ThomHPL/Open80017a/Simulations/lm13700_test.asc

I1: current; 1m
R3: res; 1Meg
R4: res; 1k
R5: res; 1k
U1: LM13700
V1: voltage; 15
V2: voltage; SINE(0 100m 1k); AC 1m
V3: voltage; -15
Named nets: 0, VCC, VSS
.lib lm13700.sub
;tran 1u 10m
.dc I1 0.05m 1m .01m
