ThomHPL/Open80017a/Simulations/open_80017A.asc

C1: cap; 100n
C2: cap; 47p
C3: cap; 100n
C4: cap; 270p
C5: cap; 270p
C6: cap; 270p
C7: cap; 270p
C8: cap; 47p
C9: cap; 1µ
C10: cap; 270p
I1: current; 37µ
Q1: pnp; 2N2907
Q2: pnp; 2N3906
Q3: pnp; 2N3906
Q4: pnp; 2N2907
R1: res; 10K
R2: res; 25k
R3: res; 23k
R4: res; 5k
R5: res; 470k
R6: res; 10k
R7: res; 22k
R8: res; 1.5Meg
R9: res; 10k
R10: res; 10K
R11: res; 12.5k
R12: res; 10k
R13: res; 8.2k
R14: res; 470k
R15: res; 560
R16: res; 5k
R17: res; 50k
R18: res; 50k
R19: res; 680k
R20: res; 560
R21: res; 68k
R22: res; 15k
R23: res; 68k
R24: res; 4.7k
R25: res; 10k
R26: res; 560
R27: res; 68k
R28: res; 15k
R29: res; 68k
R30: res; 10k
R31: res; 560
R32: res; 68k
R33: res; 15k
R34: res; 68k
R35: res; 10k
R36: res; 560
R37: res; 68k
R38: res; 15k
R39: res; 100k
R40: res; 1.5k
R41: res; 25k
R42: res; 1.5k
R43: res; 1.5k
R44: res; 47k
R45: res; 560
R46: res; 560
R47: res; 4.7k
R48: res; 82k
R49: res; 37k
R50: res; 10K
R51: res; 23k
R52: res; 5k
R53: res; 470k
R54: res; 10k
R55: res; 50
R56: res; 50
R57: res; 2.2Meg
R58: res; 15k
R59: res; 68k
R60: res; 560
R61: res; 4.7k
U1: opamp
U2: LM13700
U3: LM13700
U4: LM13700
U5: LM13700
U6: LM13700
U7: opamp
U8: opamp
U9: LM13700
U10: opamp
U11: opamp
U12: LM13700
V1: voltage; {CV_VCA}
V2: voltage; 15
V3: voltage; 15
V4: voltage; SINE(0 {IN_ampl} 440); AC 1
V5: voltage; {CV_VCF}
V6: voltage; SINE(0 .2 440); AC 1
V7: voltage; {CV_RESO}
X1: pmos; ZVP1320F
X2: pmos; ZVP1320F
X3: pmos; ZVP1320F
X4: pmos; ZVP1320F
X5: pmos; ZVP1320F
Named nets: 0, +15, -15, VCF_cont, Iabc, VCF_in, RESO_cont, VCF_out, VCA_in, VCA_cont, VCA_out
.lib opamp.sub
.lib lm13700.sub
*ZETEX ZVP1320F Spice Model v1.0 Last Revised 13/06/02
    *
    .SUBCKT ZVP1320F 3 4 5
    *                D G S
    M1 6 2 8 8 MOSMOD
    M2 6 2 8 8 MOSMODS
    RG 4 2 56
    RIN 2 8 200E6
    RD 3 6 RDSMOD 71
    RS 8 5 RDSMOD 6.6 
    RL 3 5 200E6
    C1 2 8 42E-12
    D1 3 5 DMOD1
    D2 3 17 DMOD2
    Egs1 2 17 2 8 1
    .MODEL MOSMOD PMOS VTO=-2.56 IS=1E-15 KP=.059 CBD=15E-12 PB=1 LAMBDA=4.9E-3
    .MODEL MOSMODS PMOS VTO=-2.2 IS=1E-15 KP=0.002 PB=1
    .MODEL DMOD1 D IS=2E-13 RS=0.12 N=1.01 IKF=3e-3
    .MODEL DMOD2 D CJO=18e-12 IS=1e-30 N=10
    .MODEL RDSMOD RES (TC1=8E-3 TC2=3E-5)
    .ENDS ZVP1320F
    *
    *$
    *
.ac dec 101 10 100k
.param IN_ampl=0.2 CV_VCF=1.5 CV_RESO=0.5 CV_VCA=2
CV_RESO sweep from 0 to 5V
    RESO_cont from 0 to 262uA
    ~53uA/V
Varies the Q factor of the filter
CV_VCF sweep from 0 to 3V
-3dB cutoff freq covers: 
    - at 0V RESO: 50Hz -> 19kHz
    - at 3V RESO: 185Hz -> 55kHz
References:
https://github.com/deanm1278/LM13700-spice-model
https://modwiggler.com/forum/viewtopic.php?t=238335
https://www.diodes.com/assets/Spice-Models/Discrete-Prodcut-Groups/P-Channel-100V.txt
CV_VCA unity gain at ~300mV
    20dB at 2V
    28.6dB at 5V
80017A module
Module input
    test at 200mV amplitude
JUNO 106
tested at IN_ampl=0.2 CV_VCF=1.5 CV_RESO=0.5 CV_VCA=2
;.tran 10m
