ThomHPL/Open80017a/Simulations/vca_cont_driver.asc

C1: cap; 100n
Q1: pnp; 2N2907
R1: res; 10K
R2: res; 100
R3: res; 23k
R4: res; 5k
R5: res; 470k
R6: res; 10k
R7: res; 22k
R12: res; 10k
U1: opamp
V1: voltage; PULSE(0 5 0 100m 100u 0u 100.1m)
V2: voltage; 15
V3: voltage; 15
Named nets: 0, +15, -15
.dc V1 0 5 0.1
.lib opamp.sub
